tineira/hue-simple-switch/channels.h

#pragma once

#include <WiFi.h>
#include <Preferences.h>
#include "hue.h"
#include "hue_discover.h"
#include "recipes.h"
#include "channel_input.h"

// Channels: closed = GPIO to GND (INPUT_PULLUP). The console picks each channel's kind
// (config channels[]); a pin it does not list does nothing. The old config payload has no
// channels[]: every pin runs with its compiled default kind below. D3-D5 (since 0.5.0) default
// to CHK_NONE, so a pin nobody wired never acts on the old payload either.
// D3-D5 are GPIO 21-23: no strapping pins, and this firmware has no I2C on D4/D5.

struct ChannelDef {
  const char *id;
  int gpio;
  const char *label;
  ChannelSettingKind defaultKind;
};

static const ChannelDef kChannels[] = {
    {"boot", 9, "BOOT", CHK_MOMENTARY},
    {"d0", 0, "D0", CHK_MAINTAINED},
    {"d1", 1, "D1", CHK_MAINTAINED},
    {"d2", 2, "D2", CHK_MAINTAINED},
    {"d3", 21, "D3", CHK_NONE},
    {"d4", 22, "D4", CHK_NONE},
    {"d5", 23, "D5", CHK_NONE},
};

static const size_t kChannelCount = sizeof(kChannels) / sizeof(kChannels[0]);

// Resolved from recipes + channels[] each time gRecipesGen changes (GPIO loop only).
struct ChannelMode {
  uint8_t kind;  // CHK_NONE = ignored
  bool flipToggle;  // toggle switch: each flip toggles (flip "toggle"); false = the lever sets on/off
  bool hasDoubleClick;
  bool hasHold;
};

inline ChannelRuntime gCh[kChannelCount];
inline ChannelMode gChMode[kChannelCount];
inline uint32_t gChModeGen = 0;
inline bool gChModeValid = false;
// A hold was posted and its release is not yet: the release goes to the Hue worker, which
// stops the dim cycle if the hold started one (GPIO loop only).
inline bool gHoldOpen[kChannelCount];
// A gesture is under way on some pin (pressed, bouncing, in a double-click window or a hold).
// Written by the loop each pass; an update does not start while it is set (ota.h).
inline volatile bool gInputsBusy = false;

// Register lists the pins only; the console picks each channel's kind.
inline void channelsAppendJson(String &out) {
  out += '[';
  for (size_t i = 0; i < kChannelCount; i++) {
    if (i) {
      out += ',';
    }
    out += "{\"id\":";
    jsonAppendEscaped(out, kChannels[i].id);
    out += ",\"gpio\":";
    out += String(kChannels[i].gpio);
    out += ",\"label\":";
    jsonAppendEscaped(out, kChannels[i].label);
    out += '}';
  }
  out += ']';
}

inline bool channelIsBoot(size_t i) { return strcmp(kChannels[i].id, "boot") == 0; }

#include "hue_worker.h"

// Post the event to the Hue worker; the recipe is looked up when it runs.
inline bool channelPost(size_t i, uint8_t event, uint8_t flags = 0) { return hueJobPost(i, event, flags); }

inline void channelPrime(size_t i) {
  const int v = digitalRead(kChannels[i].gpio);
  gCh[i].lastReading = v;
  gCh[i].stable = v;
  gCh[i].lastChangeMs = millis();
  gCh[i].primed = true;
  gCh[i].waitOff = false;
  gCh[i].waitEvent = HJ_OFF;
  gCh[i].waitStartMs = 0;
  gCh[i].pressStartMs = 0;
  gCh[i].longPressHandled = false;
}

inline void channelsPrime() {
  for (size_t i = 0; i < kChannelCount; i++) {
    channelPrime(i);
  }
}

// A channel whose kind or flip changed starts from the current pin state, without firing: in
// toggle mode a flip posted at boot or on a config change would turn off lights that came back
// on after a power cut.
inline void channelsResolveModes() {
  if (gChModeValid && gRecipesGen == gChModeGen) {
    return;
  }
  recipesLock();
  for (size_t i = 0; i < kChannelCount; i++) {
    const char *id = kChannels[i].id;
    uint8_t kind = gChannelsFromConsole ? recipesChannelKind(id) : kChannels[i].defaultKind;
    // BOOT is the pairing button: always a push button, even when not configured, so its
    // 3 s re-pair keeps working.
    if (channelIsBoot(i)) {
      kind = CHK_MOMENTARY;
    }
    const bool flipToggle = gChannelsFromConsole && kind == CHK_MAINTAINED && recipesChannelFlip(id) == CHF_TOGGLE;
    if (gChModeValid && (kind != gChMode[i].kind || flipToggle != gChMode[i].flipToggle)) {
      channelPrime(i);
    }
    gChMode[i].kind = kind;
    gChMode[i].flipToggle = flipToggle;
    gChMode[i].hasDoubleClick = recipesFind(id, "double_click") != nullptr;
    gChMode[i].hasHold = recipesFind(id, "hold") != nullptr;
  }
  gChModeGen = gRecipesGen;
  recipesUnlock();
  gChModeValid = true;
  for (size_t i = 0; i < kChannelCount; i++) {
    LOG("%s: %s%s%s\n", kChannels[i].id,
        gChMode[i].kind == CHK_NONE ? "not configured"
                                     : (gChMode[i].kind == CHK_MOMENTARY
                                            ? "push button"
                                            : (gChMode[i].flipToggle ? "toggle switch, each flip toggles"
                                                                     : "toggle switch")),
        gChMode[i].hasDoubleClick ? ", double-click" : "", gChMode[i].hasHold ? ", hold" : "");
  }
}

inline void channelsBegin() {
  for (size_t i = 0; i < kChannelCount; i++) {
    pinMode(kChannels[i].gpio, INPUT_PULLUP);
  }
  channelsLoadLastScenes();
  channelsPrime();
}

// Toggle switch: the rules for each flip setting are in channel_input.h (channelMaintainedStep).
inline void channelMaintained(size_t i, unsigned long now) {
  uint8_t event = 0;
  uint8_t flags = 0;
  if (channelMaintainedStep(gCh[i], digitalRead(kChannels[i].gpio), now, gChMode[i].flipToggle,
                            gChMode[i].hasDoubleClick, &event, &flags)) {
    channelPost(i, event, flags);
  }
}

inline void channelBootRePair() {
  if (WiFi.status() != WL_CONNECTED) {
    LOGLN("Re-pair skipped: WiFi down");
    return;
  }
  if (huePairBusy()) {
    return;
  }
  huePairSessionBegin();
}

// Still pressed. With a hold recipe: hold at kHoldMs (BOOT then never re-pairs from the
// button). Without one: no hold threshold, except BOOT's 3 s re-pair.
inline void channelMomentaryHeld(size_t i, unsigned long now) {
  ChannelRuntime &st = gCh[i];
  const unsigned long held = now - st.pressStartMs;
  if (gChMode[i].hasHold) {
    if (held >= kHoldMs) {
      st.longPressHandled = true;
      if (channelPost(i, HJ_HOLD, HJF_MAY_EXPIRE)) {
        gHoldOpen[i] = true;
      }
    }
    return;
  }
  if (channelIsBoot(i) && held >= kLongPressMs) {
    st.longPressHandled = true;
    channelBootRePair();
  }
}

// Push button: short on release, at once when there is no double_click recipe; otherwise a
// second press inside the window is double_click and an expired window is short.
inline void channelMomentary(size_t i, unsigned long now) {
  ChannelRuntime &st = gCh[i];
  const ChannelDef &ch = kChannels[i];
  const int reading = digitalRead(ch.gpio);

  if (reading != st.lastReading) {
    st.lastChangeMs = now;
    st.lastReading = reading;
  }

  if (st.waitOff && (now - st.waitStartMs) >= kDoubleClickMs && st.stable == HIGH &&
      st.lastReading == HIGH) {
    st.waitOff = false;
    channelPost(i, HJ_SHORT, HJF_MAY_EXPIRE);
  }

  if (st.stable == LOW && st.pressStartMs && !st.longPressHandled) {
    channelMomentaryHeld(i, now);
  }

  if ((now - st.lastChangeMs) < kDebounceMs) {
    return;
  }
  if (reading == st.stable) {
    return;
  }

  st.stable = reading;
  if (reading == LOW) {
    st.pressStartMs = now;
    st.longPressHandled = false;
    if (st.waitOff) {
      // Second press inside the window: its release and hold do nothing.
      st.waitOff = false;
      st.longPressHandled = true;
      channelPost(i, HJ_DOUBLE, HJF_MAY_EXPIRE);
    }
    return;
  }

  const bool handled = st.longPressHandled || !st.pressStartMs;
  st.pressStartMs = 0;
  if (handled) {
    return;
  }
  if (gChMode[i].hasDoubleClick) {
    st.waitOff = true;
    st.waitStartMs = now;
    return;
  }
  channelPost(i, HJ_SHORT, HJF_MAY_EXPIRE);
}

inline void channelsPoll(unsigned long now) {
  channelsResolveModes();
  bool busy = false;
  for (size_t i = 0; i < kChannelCount; i++) {
    if (!gCh[i].primed) {
      continue;
    }
    const ChannelRuntime &st = gCh[i];
    if (gChMode[i].kind != CHK_NONE &&
        (st.lastReading != st.stable || st.waitOff || gHoldOpen[i] ||
         (gChMode[i].kind == CHK_MOMENTARY && st.stable == LOW))) {
      busy = true;
    }
    if (gChMode[i].kind == CHK_MAINTAINED) {
      channelMaintained(i, now);
    } else if (gChMode[i].kind == CHK_MOMENTARY) {
      channelMomentary(i, now);
    }
    // The release queues behind its hold on this channel, so the stop always follows the start.
    if (gHoldOpen[i] && (gChMode[i].kind != CHK_MOMENTARY || gCh[i].stable == HIGH)) {
      gHoldOpen[i] = false;
      channelPost(i, HJ_RELEASE);
    }
  }
  hueWorkerLoopPoll();  // no Hue task: dim turn-arounds run here
  gInputsBusy = busy;
}
