tineira/hue-simple-switch/hue-simple-switch.ino

#if defined(__has_include)
#if __has_include("config.h")
#include "config.h"
#endif
#endif
#include "log.h"
#include <WiFi.h>

String gHueBridgeIp;
String gHueAppKey;

#include "hue.h"
#include "hue_discover.h"
#include "recipes.h"
#include "channels.h"
#include "console.h"
#include "usb.h"
#include "led.h"

// The core would confirm a freshly updated image at startup; this firmware confirms it after
// its first successful console poll instead (ota.h), so a new image that cannot get that far
// goes back to the previous one on the next restart.
extern "C" bool verifyRollbackLater() { return true; }

static bool gWifiWasUp = false;
static bool gWifiBootTried = false;
static unsigned long gWifiLastTryMs = 0;

static void usbPump(unsigned long ms) {
  const unsigned long start = millis();
  usbPoll();
  while (millis() - start < ms) {
    delay(10);
    usbPoll();
  }
}

static void afterWifiUp() {
  LOG("IP: ");
  LOGLN(WiFi.localIP());
  LOG("mac %s\n", deviceMacHex().c_str());
  if (!hueEnsureReady()) {
    LOGLN("Hue setup failed — press Bridge button if pairing, check Wi-Fi LAN");
    gHueReady = false;
    // No sync follows: let the console task's own polls register, as they would without a Bridge check.
    gConsoleBootSyncDone = true;
    return;
  }
  gHueReady = true;
  LOG("Using Bridge %s id=%s\n", gHueBridgeIp.c_str(), gHueBridgeId.c_str());
  if (recipesBindBridge(gHueBridgeId)) {
    gConsoleRegistered = false;
  }
  if (!consoleConfigured()) {
    LOGLN("console: no token/url in NVS — HUESET on USB");
  }
  // The console task reads the Bridge from the published copy: publish before asking for a sync.
  hueWorkerPublishCreds();
  gNeedConsoleSync = true;
}

void setup() {
  Serial.begin(115200);
  // USB CDC: without a PC, write() waits for the host. 100 ms: 0 dropped writes when tx_lock was busy.
  Serial.setTxTimeoutMs(100);
  usbPoll();
  usbPump(200);

  pinMode(LED_BUILTIN, OUTPUT);
  digitalWrite(LED_BUILTIN, HIGH);
  ledBegin();

  LOG("hue-simple-switch\n");
  LOG("firmware %s\n", FIRMWARE_VERSION);

  gOnHueWait = []() { usbPoll(); };

  consoleLoadNvs();
  otaBootCheck();
  recipesLoad();
  hueLoadStore();
  channelsBegin();
  hueWorkerPublishCreds();
  hueWorkerBegin();
  consoleWorkerBegin();
  usbPoll();

  // Web Serial DTR-resets the C6; Scan/ping can arrive during boot.
  // Do not WiFi.begin over an Improv scan, and keep usbPoll alive if STA fails.
  usbPump(1000);
  if (!usbWifiBusy()) {
    wifiBootConnect();
    gWifiBootTried = true;
    gWifiLastTryMs = millis();
    usbPoll();
  }

  channelsPrime();
  LOGLN("GPIO: kinds from console channels[] (defaults: boot push button, d0-d2 toggle switch, d3-d5 unused)");
}

static void huePairApplySync() {
  if (!gHuePairSync) {
    return;
  }
  gHuePairSync = false;
  if (recipesBindBridge(gHueBridgeId)) {
    gConsoleRegistered = false;
  }
  hueWorkerPublishCreds();
  gNeedConsoleSync = true;
}

void loop() {
  const unsigned long now = millis();
  usbPoll();
  huePairApplySync();
  // Pairing and HUECLR (in usbPoll) change the Bridge IP and key: hand the Hue worker and the
  // console task the new copy.
  hueWorkerPublishCreds();
  channelsPoll(now);
  const bool sta = ledPoll(now);

  if (!sta) {
    if (gWifiWasUp) {
      gWifiWasUp = false;
    }
    if (!gWifiBootTried && !usbWifiBusy()) {
      wifiBootConnect();
      gWifiBootTried = true;
      gWifiLastTryMs = now;
    }
    if (gWifiHaveCreds && !usbWifiBusy() && (now - gWifiLastTryMs >= 10000UL)) {
      gWifiLastTryMs = now;
      LOGLN("WiFi retry");
      wifiRetryStored();
    }
    return;
  }

  if (usbWifiBusy()) {
    return;
  }

  if (!gWifiWasUp) {
    gWifiWasUp = true;
    if (gHueReady) {
      gNeedConsoleSync = true;
    } else if (!huePairBusy()) {
      afterWifiUp();
    }
  }
}
